loneoceans/lume1-fw3x/anduril1/fsm-ramping.h

/*
 * fsm-ramping.h: Ramping functions for SpaghettiMonster.
 * Handles 1- to 4-channel smooth ramping on a single LED.
 *
 * Copyright (C) 2017 Selene Scriven
 *
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
 * You should have received a copy of the GNU General Public License
 * along with this program.  If not, see <http://www.gnu.org/licenses/>.
 */

#ifndef FSM_RAMPING_H
#define FSM_RAMPING_H

#ifdef USE_RAMPING

// actual_level: last ramp level set by set_level()
volatile uint8_t actual_level = 0;

#ifdef USE_TINT_RAMPING
uint8_t tint = 128;
#define USE_TRIANGLE_WAVE
#endif

#ifdef USE_SET_LEVEL_GRADUALLY
// adjust brightness very smoothly
volatile uint8_t gradual_target;
inline void set_level_gradually(uint8_t lvl);
void gradual_tick();
#endif

// auto-detect the data type for PWM tables
#ifndef PWM_BITS
#define PWM_BITS 8
#define PWM_TOP 255
#endif
#if PWM_BITS <= 8
#define PWM_DATATYPE uint8_t
#define PWM_TOP 255
#define PWM_GET(x,y) pgm_read_byte(x+y)
#else
#define PWM_DATATYPE uint16_t
#define PWM_TOP 1023  // 10 bits by default
// pointer plus 2*y bytes
//#define PWM_GET(x,y) pgm_read_word(x+(2*y))
// nope, the compiler was already doing the math correctly
#define PWM_GET(x,y) pgm_read_word(x+y)
#endif

// use UI-defined ramp tables if they exist
#ifdef PWM1_LEVELS
PROGMEM const PWM_DATATYPE pwm1_levels[] = { PWM1_LEVELS };
#endif
#ifdef PWM2_LEVELS
PROGMEM const PWM_DATATYPE pwm2_levels[] = { PWM2_LEVELS };
#endif
#ifdef PWM3_LEVELS
PROGMEM const PWM_DATATYPE pwm3_levels[] = { PWM3_LEVELS };
#endif
#ifdef PWM4_LEVELS
PROGMEM const PWM_DATATYPE pwm4_levels[] = { PWM4_LEVELS };
#endif

// default / example ramps
#ifndef PWM1_LEVELS
#if PWM_CHANNELS == 1
  #if RAMP_LENGTH == 50
    // ../../bin/level_calc.py 1 50 7135 3 0.25 980
    PROGMEM const PWM_DATATYPE pwm1_levels[] = { 3,3,3,3,4,4,4,5,5,6,7,8,9,11,12,14,16,18,20,23,25,28,32,35,39,43,47,52,57,62,68,74,80,87,94,102,110,118,127,136,146,156,167,178,189,201,214,227,241,255 };
  #elif RAMP_LENGTH == 75
    // ../../bin/level_calc.py 1 75 7135 3 0.25 980
    PROGMEM const PWM_DATATYPE pwm1_levels[] = { 3,3,3,3,3,3,4,4,4,4,5,5,5,6,6,7,8,8,9,10,11,12,13,14,15,17,18,20,21,23,25,27,29,31,33,36,38,41,44,47,50,53,56,59,63,67,71,75,79,83,88,93,98,103,108,113,119,125,131,137,143,150,157,164,171,178,186,194,202,210,219,227,236,246,255 };
  #elif RAMP_LENGTH == 150
    // ../../bin/level_calc.py 1 150 7135 3 0.25 980
    PROGMEM const PWM_DATATYPE pwm1_levels[] = { 3,3,3,3,3,3,3,3,3,3,3,4,4,4,4,4,4,4,4,4,5,5,5,5,5,6,6,6,6,7,7,7,8,8,8,9,9,9,10,10,11,11,12,12,13,13,14,15,15,16,17,17,18,19,19,20,21,22,23,24,24,25,26,27,28,29,31,32,33,34,35,36,38,39,40,42,43,44,46,47,49,50,52,53,55,57,58,60,62,64,66,68,70,72,74,76,78,80,82,84,86,89,91,93,96,98,101,103,106,109,111,114,117,120,123,125,128,131,134,138,141,144,147,151,154,157,161,164,168,171,175,179,183,186,190,194,198,202,206,210,215,219,223,228,232,236,241,246,250,255 };
  #endif
#elif PWM_CHANNELS == 2
  #if RAMP_LENGTH == 50
    // ../../bin/level_calc.py 2 50 7135 4 0.33 150 FET 1 10 1500
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
  4-channel PWM not really supported yet, sorry.
#endif
#endif

// RAMP_SIZE / MAX_LVL
#define RAMP_SIZE (sizeof(pwm1_levels)/sizeof(PWM_DATATYPE))
#define MAX_LEVEL RAMP_SIZE

void set_level(uint8_t level);
//void set_level_smooth(uint8_t level);

#endif  // ifdef USE_RAMPING
#endif
