loneoceans/lume1-fw3x/anduril1/fsm-adc.h

/*
 * fsm-adc.h: ADC (voltage, temperature) functions for SpaghettiMonster.
 *
 * Copyright (C) 2017 Selene Scriven
 *
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
 * You should have received a copy of the GNU General Public License
 * along with this program.  If not, see <http://www.gnu.org/licenses/>.
 */

#ifndef FSM_ADC_H
#define FSM_ADC_H


#if defined(USE_LVP) || defined(USE_THERMAL_REGULATION)
// use raw value instead of lowpassed value for the next N measurements
// (2 = 1 for voltage + 1 for temperature)
volatile uint8_t adc_reset = 2;
#endif

#ifdef USE_LVP
// default 5 seconds between low-voltage warning events
#ifndef VOLTAGE_WARNING_SECONDS
#define VOLTAGE_WARNING_SECONDS 5
#endif
// low-battery threshold in volts * 10
#ifndef VOLTAGE_LOW
#define VOLTAGE_LOW 29
#endif
// MCU sees voltage 0.X volts lower than actual, add X/2 to readings
#ifndef VOLTAGE_FUDGE_FACTOR
#ifdef USE_VOLTAGE_DIVIDER
#define VOLTAGE_FUDGE_FACTOR 0
#else
#define VOLTAGE_FUDGE_FACTOR 5
#endif
#endif

volatile uint8_t irq_adc = 0;  // ADC interrupt happened?
uint8_t adc_sample_count = 0;  // skip the first sample; it's junk
uint8_t adc_channel = 0;  // 0=voltage, 1=temperature
uint16_t adc_raw[2];  // last ADC measurements (0=voltage, 1=temperature)
uint16_t adc_smooth[2];  // lowpassed ADC measurements (0=voltage, 1=temperature)
// ADC code is split into two parts:
// - ISR: runs immediately at each interrupt, does the bare minimum because time is critical here
// - deferred: the bulk of the logic runs later when time isn't so critical
uint8_t adc_deferred_enable = 0;  // stop waiting and run the deferred code
void adc_deferred();  // do the actual ADC-related calculations

static inline void ADC_voltage_handler();
volatile uint8_t voltage = 0;
#ifdef USE_LVP
void low_voltage();
#endif

#ifdef USE_BATTCHECK
void battcheck();
#ifdef BATTCHECK_VpT
#define USE_BLINK_NUM
#endif
#if defined(BATTCHECK_8bars) || defined(BATTCHECK_6bars) || defined(BATTCHECK_4bars)
#define USE_BLINK_DIGIT
#endif
#endif
#endif  // ifdef USE_LVP


#ifdef USE_THERMAL_REGULATION
// try to keep temperature below 45 C
#ifndef DEFAULT_THERM_CEIL
#define DEFAULT_THERM_CEIL 45
#endif
// don't allow user to set ceiling above 70 C
#ifndef MAX_THERM_CEIL
#define MAX_THERM_CEIL 70
#endif
// Local per-MCU calibration value
#ifndef THERM_CAL_OFFSET
#define THERM_CAL_OFFSET 0
#endif
// temperature now, in C (ish)
volatile int16_t temperature;
uint8_t therm_ceil = DEFAULT_THERM_CEIL;
int8_t therm_cal_offset = 0;
static inline void ADC_temperature_handler();
#endif  // ifdef USE_THERMAL_REGULATION


inline void ADC_on();
inline void ADC_off();
inline void ADC_start_measurement();


#endif
