loneoceans/lume1-fw3x/anduril1/fsm-misc.c

/*
 * fsm-misc.c: Miscellaneous function for SpaghettiMonster.
 *
 * Copyright (C) 2017 Selene Scriven
 *
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
 * You should have received a copy of the GNU General Public License
 * along with this program.  If not, see <http://www.gnu.org/licenses/>.
 */

#ifndef FSM_MISC_C
#define FSM_MISC_C


#ifdef USE_DYNAMIC_UNDERCLOCKING
void auto_clock_speed() {
    uint8_t level = actual_level;  // volatile, avoid repeat access
    if (level < QUARTERSPEED_LEVEL) {
        // run at quarter speed
        // note: this only works when executed as two consecutive instructions
        // (don't try to combine them or put other stuff between)
        clock_prescale_set(clock_div_4);
    }
    else if (level < HALFSPEED_LEVEL) {
        // run at half speed
        clock_prescale_set(clock_div_2);
    } else {
        // run at full speed
        clock_prescale_set(clock_div_1);
    }
}
#endif

#if defined(USE_BLINK_NUM) || defined(USE_BLINK_DIGIT)
#define BLINK_SPEED 1000
uint8_t blink_digit(uint8_t num) {
    //StatePtr old_state = current_state;

    // "zero" digit gets a single short blink
    uint8_t ontime = BLINK_SPEED * 2 / 12;
    if (!num) { ontime = 8; num ++; }

    for (; num>0; num--) {
        set_level(BLINK_BRIGHTNESS);
        nice_delay_ms(ontime);
        set_level(0);
        nice_delay_ms(BLINK_SPEED * 3 / 12);
    }
    return nice_delay_ms(BLINK_SPEED * 8 / 12);
}
#endif

#ifdef USE_BLINK_BIG_NUM
uint8_t blink_big_num(uint16_t num) {
    uint16_t digits[] = { 10000, 1000, 100, 10, 1 };
    uint8_t started = 0;
    for (uint8_t digit=0; digit<sizeof(digits)/sizeof(uint16_t); digit++) {
        uint16_t scale = digits[digit];
        if (num >= scale) {
            started = 1;
        }
        if (started) {
            uint8_t digit = 0;
            while (num >= scale) {
                num -= scale;
                digit ++;
            }
            if (! blink_digit(digit)) return 0;
        }
    }

    return nice_delay_ms(1000);
}
#endif
#ifdef USE_BLINK_NUM
uint8_t blink_num(uint8_t num) {
    //StatePtr old_state = current_state;
    #if 0
    uint8_t hundreds = num / 100;
    num = num % 100;
    uint8_t tens = num / 10;
    num = num % 10;
    #else  // 8 bytes smaller
    uint8_t hundreds = 0;
    uint8_t tens = 0;
    for(; num >= 100; hundreds ++, num -= 100);
    for(; num >= 10; tens ++, num -= 10);
    #endif

    #if 0
    // wait a moment in the dark before starting
    set_level(0);
    nice_delay_ms(200);
    #endif

    #if 0
    if (hundreds) {
        if (! blink_digit(hundreds)) return 0;
        if (! blink_digit(tens)) return 0;
    }
    else if (tens) {
        if (! blink_digit(tens)) return 0;
    }
    if (! blink_digit(num)) return 0;
    return nice_delay_ms(1000);
    #else // same size :(
    if (hundreds) if (! blink_digit(hundreds)) return 0;
    if (hundreds || tens) if (! blink_digit(tens)) return 0;
    if (! blink_digit(num)) return 0;
    return nice_delay_ms(1000);
    #endif

    /*
    uint8_t volts, tenths;
    volts = voltage / 10;
    tenths = voltage % 10;
    if (! blink(volts)) return;
    nice_delay_ms(200);
    if (! blink(tenths)) return;
    nice_delay_ms(200);
    */
}
#endif

#ifdef USE_INDICATOR_LED
void indicator_led(uint8_t lvl) {
    switch (lvl) {
        case 0:  // indicator off
            DDRB &= 0xff ^ (1 << AUXLED_PIN);
            PORTB &= 0xff ^ (1 << AUXLED_PIN);
            #ifdef AUXLED2_PIN  // second LED mirrors the first
            DDRB &= 0xff ^ (1 << AUXLED2_PIN);
            PORTB &= 0xff ^ (1 << AUXLED2_PIN);
            #endif
            break;
        case 1:  // indicator low
            DDRB &= 0xff ^ (1 << AUXLED_PIN);
            PORTB |= (1 << AUXLED_PIN);
            #ifdef AUXLED2_PIN  // second LED mirrors the first
            DDRB &= 0xff ^ (1 << AUXLED2_PIN);
            PORTB |= (1 << AUXLED2_PIN);
            #endif
            break;
        default:  // indicator high
            DDRB |= (1 << AUXLED_PIN);
            PORTB |= (1 << AUXLED_PIN);
            #ifdef AUXLED2_PIN  // second LED mirrors the first
            DDRB |= (1 << AUXLED2_PIN);
            PORTB |= (1 << AUXLED2_PIN);
            #endif
            break;
    }
}

/*
void indicator_led_auto() {
    if (actual_level > MAX_1x7135) indicator_led(2);
    else if (actual_level > 0) indicator_led(1);
    else indicator_led(0);
}
*/
#endif  // USE_INDICATOR_LED

#ifdef USE_BUTTON_LED
// TODO: Refactor this and RGB LED function to merge code and save space
void button_led_set(uint8_t lvl) {
    switch (lvl) {
        case 0:  // LED off
            BUTTON_LED_DDR  &= 0xff ^ (1 << BUTTON_LED_PIN);
            BUTTON_LED_PUE  &= 0xff ^ (1 << BUTTON_LED_PIN);
            BUTTON_LED_PORT &= 0xff ^ (1 << BUTTON_LED_PIN);
            break;
        case 1:  // LED low
            BUTTON_LED_DDR  &= 0xff ^ (1 << BUTTON_LED_PIN);
            BUTTON_LED_PUE  |= (1 << BUTTON_LED_PIN);
            BUTTON_LED_PORT |= (1 << BUTTON_LED_PIN);
            break;
        default:  // LED high
            BUTTON_LED_DDR  |= (1 << BUTTON_LED_PIN);
            BUTTON_LED_PUE  |= (1 << BUTTON_LED_PIN);
            BUTTON_LED_PORT |= (1 << BUTTON_LED_PIN);
            break;
    }
}
#endif

#ifdef USE_AUX_RGB_LEDS
void rgb_led_set(uint8_t value) {
    // value: 0b00BBGGRR
    uint8_t pins[] = { AUXLED_R_PIN, AUXLED_G_PIN, AUXLED_B_PIN };
    for (uint8_t i=0; i<3; i++) {
        uint8_t lvl = (value >> (i<<1)) & 0x03;
        uint8_t pin = pins[i];
        switch (lvl) {
            case 0:  // LED off
                AUXLED_RGB_DDR  &= 0xff ^ (1 << pin);
                AUXLED_RGB_PUE  &= 0xff ^ (1 << pin);
                AUXLED_RGB_PORT &= 0xff ^ (1 << pin);
                break;
            case 1:  // LED low
                AUXLED_RGB_DDR  &= 0xff ^ (1 << pin);
                AUXLED_RGB_PUE  |= (1 << pin);
                AUXLED_RGB_PORT |= (1 << pin);
                break;
            default:  // LED high
                AUXLED_RGB_DDR  |= (1 << pin);
                AUXLED_RGB_PUE  |= (1 << pin);
                AUXLED_RGB_PORT |= (1 << pin);
                break;
        }
    }
}
#endif  // ifdef USE_AUX_RGB_LEDS

#ifdef USE_TRIANGLE_WAVE
uint8_t triangle_wave(uint8_t phase) {
    uint8_t result = phase << 1;
    if (phase > 127) result = 255 - result;
    return result;
}
#endif

#ifdef USE_REBOOT
void reboot() {
    // put the WDT in hard reset mode, then trigger it
    cli();
    #if (ATTINY == 25) || (ATTINY == 45) || (ATTINY == 85)
        WDTCR = 0xD8 | WDTO_15MS;
    #elif (ATTINY == 1634)
        // allow protected configuration changes for next 4 clock cycles
        CCP = 0xD8;  // magic number
        // reset (WDIF + WDE), no WDIE, fastest (16ms) timing (0000)
        // (DS section 8.5.2 and table 8-4)
        WDTCSR = 0b10001000;
    #endif
    sei();
    wdt_reset();
    while (1) {}
}
#endif

#endif
