loneoceans/lume1-fw3x/anduril1/version.h

// this file is replaced automatically by the build script
// set your own date here if you're not using the build script
// otherwise, default to first human contact with the moon
#define VERSION_NUMBER "20200224"
